KipCrossing/OpenEM/Testing/veranda/03/out.csv

i0 | i1 | i2 | i3 | i4 | i5 | i6 | i7 | i8 | i9
-2831.375 | 9287.625 | 17776.62 | 19482.62 | 13771.62 | 2856.625 | -9275.374 | -17729.37 | -19516.37 | -13822.37
18605.0 | 19074.0 | 12272.0 | 719.0 | -11310.0 | -18705.0 | -18879.0 | -12102.0 | -667.0 | 10993.0
10300.75 | -1588.25 | -12821.25 | -19103.25 | -18389.25 | -10512.25 | 1608.75 | 12986.75 | 19218.75 | 18299.75
3743.25 | 14524.25 | 19655.25 | 17359.25 | 8335.25 | -3752.75 | -14384.75 | -19630.75 | -17404.75 | -8443.75
-19773.5 | -16054.5 | -6289.5 | 5898.5 | 16090.5 | 19788.5 | 16037.5 | 6076.5 | -5927.5 | -15846.5
-4180.5 | 8013.499 | 17289.5 | 19716.5 | 14616.5 | 4064.5 | -8095.5 | -17053.5 | -19634.5 | -14736.5
18289.25 | 19406.25 | 12981.25 | 1858.25 | -10083.75 | -18036.75 | -19311.75 | -13187.75 | -2000.75 | 10086.25
11343.37 | -428.625 | -11858.62 | -18870.62 | -18729.62 | -11461.63 | 391.375 | 11910.37 | 19004.37 | 18699.37
13658.12 | 19540.12 | 18004.12 | 9536.124 | -2684.875 | -13589.87 | -19384.87 | -17911.87 | -9648.875 | 2482.125
-16816.25 | -7430.25 | 4844.75 | 15111.75 | 19589.75 | 16889.75 | 7500.75 | -4743.25 | -15080.25 | -19867.25
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
