KipCrossing/OpenEM/Testing/veranda/03/RF_calibrate.csv

Freq | Amp | Shift | tim_freq | temp
9240 | 170985 | 2.391 | 92409.24 | 23.66216
Hp | 171230.9 | 2.398835
