KipCrossing/OpenEM/Testing/veranda/04/OpenEM_data.csv

ID | Amp | Shift | Shift_out | Voltage | Temp | Humidity | CoreTemp | Hs | Hp | Wmean
0 | 504.6539 | 2.1515 | 9.869001 | 13.57218 | 20.96514 | 32.60242 | 40.24 | -502.9455 | -41.49047 | 1303274.0
1 | 278.8431 | 5.26171 | 2.979211 | 13.54805 | 20.96514 | 32.69398 | 40.56 | 82.69599 | 266.2984 | 1303029.0
2 | 109.1217 | 2.63798 | 0.3554819 | 13.53081 | 20.95178 | 32.66346 | 40.56 | -106.4111 | 24.17083 | 1303217.0
3 | 244.9536 | 4.97154 | 2.689041 | 13.53771 | 20.95178 | 32.66346 | 40.56 | 29.0268 | 243.2277 | 1302957.0
4 | 349.056 | 4.01746 | 1.734961 | 13.5446 | 20.93843 | 32.66193 | 39.92 | -161.3998 | 309.5 | 1303256.0
5 | 332.355 | 4.02089 | 1.738391 | 13.53081 | 20.90906 | 32.62989 | 40.88 | -153.0419 | 295.022 | 1303031.0
6 | 464.7512 | 4.651 | 2.368501 | 13.55839 | 20.90906 | 32.59785 | 40.88 | -38.35556 | 463.1658 | 1303068.0
7 | 292.5992 | 4.19723 | 1.914732 | 13.53081 | 20.90906 | 32.62989 | 40.88 | -105.1902 | 273.0371 | 1303009.0
8 | 395.6666 | 5.59753 | 3.315031 | 13.5446 | 20.89571 | 32.61158 | 40.88 | 193.88 | 344.9096 | 1303071.0
9 | 464.0008 | 4.47576 | 2.193261 | 13.57218 | 20.89571 | 32.58106 | 40.88 | -88.87419 | 455.4098 | 1302808.0
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
