KipCrossing/OpenEM/Testing/veranda/04/out.csv

i0 | i1 | i2 | i3 | i4 | i5 | i6 | i7 | i8 | i9
-13719.25 | -2996.25 | 9095.75 | 17725.75 | 19400.75 | 13706.75 | 2811.75 | -9186.25 | -17532.25 | -19307.25
10990.75 | 18447.75 | 18866.75 | 12147.75 | 730.75 | -11037.25 | -18584.25 | -18844.25 | -12016.25 | -702.25
18249.75 | 10207.75 | -1825.25 | -12827.25 | -18993.25 | -18078.25 | -10408.25 | 1640.75 | 12845.75 | 19187.75
3835.875 | 14440.88 | 19539.88 | 17215.87 | 8152.875 | -3937.125 | -14459.12 | -19465.12 | -17126.13 | -8198.125
19720.75 | 15868.75 | 5865.75 | -6142.25 | -15823.25 | -19450.25 | -15833.25 | -6090.25 | 5914.75 | 15968.75
-3826.625 | 8238.376 | 17219.37 | 19406.37 | 14391.37 | 3951.375 | -8216.624 | -17145.62 | -19636.63 | -14381.62
-18168.5 | -19202.5 | -12824.5 | -1538.5 | 10283.5 | 18195.5 | 19039.5 | 12858.5 | 1581.5 | -10224.5
-11022.0 | 635.0 | 12018.0 | 18963.0 | 18608.0 | 11014.0 | -733.0 | -12188.0 | -18875.0 | -18420.0
13926.5 | 19362.5 | 17543.5 | 8981.5 | -2875.5 | -13783.5 | -19352.5 | -17652.5 | -9055.5 | 2905.5
16413.25 | 6835.25 | -5150.75 | -15235.75 | -19508.75 | -16539.75 | -7008.75 | 5219.25 | 15383.25 | 19593.25
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
