KipCrossing/OpenEM/Testing/veranda/04/RF_calibrate.csv

Freq | Amp | Shift | tim_freq | temp
9230 | 171627 | 2.258 | 92307.69 | 21.05058
Hp | 171790.3 | 2.282499
