KipCrossing/OpenEM/Testing/veranda/05/OpenEM_data.csv

ID | Amp | Shift | Shift_out | Voltage | Temp | Humidity | CoreTemp | Hs | Hp | Wmean
0 | 365.0935 | 2.01394 | 9.742577 | 13.53081 | 18.15595 | 36.35309 | 38.64 | -360.3283 | -58.79435 | 1295978.0
1 | 259.9996 | 0.8359402 | 8.564577 | 13.53081 | 18.12925 | 36.35157 | 38.32 | -161.2306 | -203.9718 | 1296086.0
2 | 594.0989 | 0.5724001 | 8.301037 | 13.52392 | 18.12925 | 36.35157 | 38.64 | -286.5484 | -520.4262 | 1296431.0
3 | 720.9425 | 9.88171 | 7.610347 | 13.53081 | 18.08652 | 36.36225 | 38.64 | -49.94514 | -719.2104 | 1296140.0
4 | 288.9414 | 0.4888716 | 8.217508 | 13.51013 | 18.1426 | 36.31189 | 38.64 | -125.8938 | -260.0729 | 1296431.0
5 | 691.9755 | 0.2562599 | 7.984897 | 13.51702 | 18.09987 | 36.34851 | 38.96 | -207.5776 | -660.1072 | 1296259.0
6 | 751.5757 | 0.4098492 | 8.138487 | 13.51013 | 18.07317 | 36.31952 | 38.96 | -293.4896 | -691.9031 | 1296487.0
7 | 1003.587 | 9.89526 | 7.623897 | 13.46876 | 18.08652 | 36.27985 | 38.96 | -78.04741 | -1000.548 | 1296374.0
8 | 976.2518 | 0.15275 | 7.881387 | 13.53081 | 18.08652 | 36.29358 | 39.28 | -231.7092 | -948.3556 | 1296630.0
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
