KipCrossing/OpenEM/Testing/veranda/05/RF_calibrate.csv

Freq | Amp | Shift | tim_freq | temp
9256 | 169963 | 2.29 | 92561.98 | 18.15595
Hp | 170780.4 | 2.271363
