KipCrossing/OpenEM/Testing/veranda/06/OpenEM_data.csv

ID | Amp | Shift | Shift_out | Voltage | Temp | Humidity | CoreTemp | Hs | Hp | Wmean
0 | 55075.06 | 0.3618498 | 0.3618498 | 12.98614 | 21.77958 | 40.53407 | 42.16 | -53657.74 | 12414.1 | 1301681.0
1 | 55323.97 | 0.3590803 | 0.3590803 | 12.97925 | 21.77958 | 40.53407 | 42.16 | -53921.85 | 12376.39 | 1301405.0
2 | 55229.5 | 0.3468809 | 0.3468809 | 12.95167 | 21.77958 | 40.56458 | 42.16 | -53922.9 | 11942.29 | 1301936.0
3 | 55297.14 | 0.3640001 | 0.3640001 | 12.94478 | 21.80895 | 40.63478 | 42.8 | -53857.21 | 12536.93 | 1301509.0
4 | 55235.7 | 0.3609898 | 0.3609898 | 12.94822 | 21.80895 | 40.59358 | 42.8 | -53820.95 | 12421.23 | 1302010.0
5 | 54937.93 | 0.3691707 | 0.3691707 | 12.96546 | 21.82231 | 40.62409 | 42.16 | -53466.61 | 12629.26 | 1301631.0
6 | 55257.71 | 0.3538804 | 0.3538804 | 12.96546 | 21.80895 | 40.53864 | 42.48 | -53897.37 | 12185.54 | 1301890.0
7 | 54835.28 | 0.3634501 | 0.3634501 | 12.95167 | 21.84901 | 40.50202 | 42.16 | -53411.67 | 12413.76 | 1301641.0
8 | 55273.54 | 0.3632 | 0.3632 | 12.93788 | 21.82231 | 40.48371 | 42.16 | -53840.52 | 12504.52 | 1301947.0
9 | 54762.24 | 0.3648 | 0.3648 | 12.93099 | 21.83566 | 40.48676 | 42.16 | -53330.0 | 12442.46 | 1301665.0
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
