KipCrossing/OpenEM/Testing/veranda/06/RF_calibrate.csv

Freq | Amp | Shift | tim_freq | temp
9003 | 55239 | 0.358 | 90032.16 | 21.76623
