KipCrossing/OpenEM/Testing/veranda/07/OpenEM_data.csv

ID | Amp | Shift | Shift_out | Voltage | Temp | Humidity | CoreTemp | Hs | Hp | Wmean
0 | 55153.86 | 0.3986502 | 0.3986502 | 12.47595 | 23.94522 | 43.19219 | 44.72 | -53432.71 | 13670.89 | 1315382.0
1 | 55177.61 | 0.3985901 | 0.3985901 | 12.48974 | 23.93187 | 43.17541 | 44.72 | -53456.23 | 13674.76 | 1315152.0
2 | 55202.72 | 0.4016297 | 0.4016297 | 12.51042 | 23.95857 | 43.16625 | 44.72 | -53454.34 | 13783.1 | 1315230.0
3 | 55266.44 | 0.39904 | 0.39904 | 12.50353 | 24.0013 | 43.18456 | 45.36 | -53538.42 | 13711.91 | 1315123.0
4 | 55273.61 | 0.4010897 | 0.4010897 | 12.48284 | 23.9746 | 43.17998 | 45.36 | -53527.66 | 13782.64 | 1315268.0
5 | 55354.38 | 0.4040103 | 0.4040103 | 12.48284 | 23.9746 | 43.08385 | 45.36 | -53580.46 | 13901.13 | 1315127.0
6 | 55339.76 | 0.4022593 | 0.4022593 | 12.48974 | 24.028 | 43.11895 | 46.0 | -53581.57 | 13838.51 | 1315339.0
7 | 55324.94 | 0.4029896 | 0.4029896 | 12.49663 | 24.01465 | 43.0747 | 45.68 | -53560.86 | 13859.39 | 1315190.0
8 | 55451.03 | 0.4025106 | 0.4025106 | 12.48284 | 24.028 | 43.10522 | 45.36 | -53687.11 | 13874.82 | 1315379.0
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
