KipCrossing/OpenEM/Testing/veranda/07/RF_calibrate.csv

Freq | Amp | Shift | tim_freq | temp
9004 | 55055 | 0.397 | 90032.16 | 23.91852
