KipCrossing/OpenEM/Testing/veranda/08/OpenEM_data.csv

ID | Amp | Shift | Shift_out | Voltage | Temp | Humidity | CoreTemp | Hs | Hp | Wmean
0 | 184668.3 | 1.3105 | 1.3105 | 13.25158 | 24.60479 | 38.6389 | 39.28 | -125523.2 | 135448.4 | 1303020.0
1 | 184858.1 | 1.310061 | 1.310061 | 13.25503 | 24.59144 | 38.55497 | 39.92 | -125689.8 | 135553.0 | 1302961.0
2 | 184663.0 | 1.30923 | 1.30923 | 13.22056 | 24.57809 | 38.53819 | 39.6 | -125627.7 | 135344.4 | 1303162.0
3 | 184486.1 | 1.310181 | 1.310181 | 13.22745 | 24.56474 | 38.63432 | 39.6 | -125426.6 | 135289.7 | 1303014.0
4 | 184298.9 | 1.31014 | 1.31014 | 13.22056 | 24.60479 | 38.66636 | 40.24 | -125302.8 | 135149.2 | 1303344.0
5 | 184068.2 | 1.30898 | 1.30898 | 13.19643 | 24.57809 | 38.77623 | 40.56 | -125244.3 | 134888.7 | 1303168.0
6 | 184147.5 | 1.30695 | 1.30695 | 13.19987 | 24.57809 | 38.83116 | 40.88 | -125470.2 | 134786.9 | 1303441.0
7 | 184002.4 | 1.30775 | 1.30775 | 13.21366 | 24.56474 | 38.81742 | 40.88 | -125303.6 | 134743.7 | 1303238.0
8 | 184056.0 | 1.304939 | 1.304939 | 13.21021 | 24.57809 | 38.78996 | 40.88 | -125578.0 | 134561.5 | 1303679.0
9 | 184081.4 | 1.304361 | 1.304361 | 13.22745 | 24.57809 | 38.78996 | 40.56 | -125644.2 | 134534.3 | 1303412.0
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
