KipCrossing/OpenEM/Testing/veranda/08/RF_calibrate.csv

Freq | Amp | Shift | tim_freq | temp
9151 | 185114 | 1.314 | 91503.27 | 24.63416
