KipCrossing/OpenEM/Testing/veranda/09/OpenEM_data.csv

ID | Amp | Shift | Shift_out | Voltage | Temp | Humidity | CoreTemp | Hs | Hp | Wmean
0 | 164141.5 | 1.11001 | 1.11001 | 13.25503 | 20.71412 | 36.28901 | 40.56 | -125812.7 | 105421.1 | 1302090.0
1 | 164186.9 | 1.11056 | 1.11056 | 13.19987 | 20.68475 | 36.24323 | 40.88 | -125811.0 | 105493.8 | 1301747.0
2 | 164271.8 | 1.11013 | 1.11013 | 13.22745 | 20.67139 | 36.28443 | 40.56 | -125904.6 | 105514.3 | 1301945.0
3 | 164369.8 | 1.11221 | 1.11221 | 13.24124 | 20.65537 | 36.29663 | 41.52 | -125841.6 | 105741.8 | 1301805.0
4 | 164403.0 | 1.11198 | 1.11198 | 13.24124 | 20.64202 | 36.29663 | 40.88 | -125882.3 | 105745.0 | 1301841.0
5 | 164455.1 | 1.11226 | 1.11226 | 13.21366 | 20.61265 | 36.22339 | 41.2 | -125903.6 | 105800.6 | 1301592.0
6 | 164585.4 | 1.1125 | 1.1125 | 13.22745 | 20.58594 | 36.27527 | 41.2 | -125987.3 | 105903.4 | 1301644.0
7 | 164570.8 | 1.11305 | 1.11305 | 13.18608 | 20.55657 | 36.34241 | 41.52 | -125939.5 | 105937.6 | 1301501.0
8 | 164638.1 | 1.112949 | 1.112949 | 13.21366 | 20.55657 | 36.35614 | 41.2 | -125997.8 | 105972.9 | 1301710.0
9 | 164591.0 | 1.11232 | 1.11232 | 13.24124 | 20.52987 | 36.32563 | 41.2 | -126003.6 | 105892.8 | 1301445.0
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
