KipCrossing/OpenEM/Testing/veranda/09/RF_calibrate.csv

Freq | Amp | Shift | tim_freq | temp
9151 | 163735 | 1.107 | 91503.27 | 20.74082
