KipCrossing/OpenEM/Testing/veranda/10/OpenEM_data.csv

ID | Amp | Shift | Shift_out | Voltage | Temp | Humidity | CoreTemp | Hs | Hp | Wmean
0 | 160160.4 | 1.0684 | 1.0684 | 12.60694 | 19.95575 | 36.23255 | 39.6 | -125408.2 | 99619.92 | 1300230.0
1 | 160151.7 | 1.070169 | 1.070169 | 12.62073 | 19.93973 | 36.25696 | 39.6 | -125290.6 | 99753.86 | 1300025.0
2 | 160272.2 | 1.07519 | 1.07519 | 12.59315 | 19.93973 | 36.2295 | 40.24 | -125069.3 | 100223.9 | 1300469.0
3 | 160289.8 | 1.0713 | 1.0713 | 12.59315 | 19.897 | 36.25544 | 40.24 | -125327.6 | 99928.9 | 1300078.0
4 | 160504.3 | 1.07135 | 1.07135 | 12.60005 | 19.88365 | 36.27985 | 40.56 | -125492.3 | 100066.6 | 1300304.0
5 | 160324.3 | 1.07354 | 1.07354 | 12.59315 | 19.8703 | 36.29358 | 40.56 | -125213.9 | 100126.8 | 1299909.0
6 | 160572.7 | 1.07135 | 1.07135 | 12.56558 | 19.85428 | 36.29206 | 40.88 | -125545.8 | 100109.2 | 1300100.0
7 | 160455.0 | 1.072411 | 1.072411 | 12.57247 | 19.84093 | 36.33326 | 40.88 | -125387.0 | 100119.5 | 1299672.0
8 | 160555.6 | 1.07139 | 1.07139 | 12.55179 | 19.84093 | 36.27832 | 40.88 | -125529.9 | 100101.8 | 1300098.0
9 | 160641.4 | 1.07371 | 1.07371 | 12.58626 | 19.82758 | 36.30274 | 40.56 | -125450.8 | 100338.2 | 1299822.0
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
