KipCrossing/OpenEM/Testing/veranda/10/RF_calibrate.csv

Freq | Amp | Shift | tim_freq | temp
9151 | 159524 | 1.067 | 91503.27 | 19.98245
