KipCrossing/OpenEM/Testing/veranda/11/OpenEM_data.csv

ID | Amp | Shift | Shift_out | Voltage | Temp | Humidity | CoreTemp | Hs | Hp | Wmean
0 | 157705.7 | 0.990139 | 0.990139 | 12.21395 | 17.62455 | 55.04387 | 33.84 | -128158.5 | 91904.82 | 1287935.0
1 | 157675.5 | 0.9905699 | 0.9905699 | 12.1519 | 17.6112 | 55.00725 | 34.16 | -128109.0 | 91921.89 | 1287661.0
2 | 157725.5 | 0.9898496 | 0.9898496 | 12.10364 | 17.57915 | 55.22392 | 33.84 | -128191.3 | 91893.05 | 1288008.0
3 | 157703.6 | 0.98947 | 0.98947 | 12.06917 | 17.59785 | 55.10948 | 33.84 | -128195.4 | 91849.73 | 1287691.0
4 | 157745.7 | 0.9878702 | 0.9878702 | 12.10364 | 17.57915 | 55.1873 | 34.48 | -128321.9 | 91745.27 | 1288115.0
5 | 157512.3 | 0.9879099 | 0.9879099 | 12.04849 | 17.57915 | 55.39788 | 34.48 | -128129.7 | 91612.72 | 1287585.0
6 | 157481.7 | 0.9882598 | 0.9882598 | 12.08296 | 17.5391 | 55.51995 | 34.48 | -128084.7 | 91623.08 | 1287988.0
7 | 157536.2 | 0.9882889 | 0.9882889 | 12.09675 | 17.52308 | 55.49401 | 34.16 | -128127.4 | 91657.14 | 1287803.0
8 | 157650.1 | 0.9839699 | 0.9839699 | 12.12433 | 17.52308 | 55.43756 | 34.48 | -128468.4 | 91375.1 | 1288035.0
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
