KipCrossing/OpenEM/Testing/veranda/11/RF_calibrate.csv

Freq | Amp | Shift | tim_freq | temp
9151 | 157947 | 0.992 | 91503.27 | 17.6379
