KipCrossing/OpenEM/Testing/Calibrate_data.csv

ID | Amp | Shift | Shift_out | Voltage | Temp | Humidity | Hs | Hp | Hs | Hp | amp*math.sin(math.pi*2*sft_out/spw) | 5.7 | 2.19 | Hs2 | Hp2 | 2
0 | 11150.13 | 5.900001 | 9.5 | 11.95856 | 19.98245 | 36.89784 | 10604.4 | -3445.579 | 9414.36988588912 | 5974.53250627729 |  |  |  | 5682.11807191224 | 1846.23207788523
1 | 11110.75 | 5.9 | 9.5 | 11.92409 | 19.9691 | 36.91005 | 10566.95 | -3433.41 | 9381.11649827152 | 5953.43756231288 |  |  |  | 5662.05558799399 | 1839.71338170484
2 | 11330.16 | 5.91 | 9.51 | 11.95856 | 19.9691 | 36.99397 | 10797.41 | -3433.437 | 9604.32664431377 | 6010.77659998479 |  |  |  | 5716.58825340996 | 1857.43211878656
3 | 11312.82 | 5.9 | 9.5 | 11.94822 | 19.9691 | 36.91005 | 10759.13 | -3495.853 | 9551.72984217771 | 6061.71208277428 |  |  |  | 5765.03077622755 | 1873.17204858521
4 | 11241.93 | 5.9 | 9.5 | 11.93788 | 19.9691 | 36.92531 | 10691.71 | -3473.947 | 9491.87543553888 | 6023.72732127822 |  |  |  | 5728.9051212868 | 1861.43411175565
5 | 11461.74 | 5.89 | 9.49 | 11.95856 | 19.98245 | 36.89784 | 10878.29 | -3610.294 | 9638.68815671021 | 6202.1911003527 |  |  |  | 5898.63426129824 | 1916.58245237004
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
