KipCrossing/OpenEM/Testing/Lara/OpenEM_data.csv

ID | Amp | Shift | Shift_out | Voltage | Temp | Humidity | CoreTemp | Hs | Hp
0 | 5385.1 | 9.51 | 0.2200003 | 11.93099 | 25.33646 | 17.12978 | 34.48 | 742.0154 | 5333.734
1 | 5811.45 | 9.559999 | 0.2699995 | 11.77241 | 25.36317 | 17.07942 | 35.44 | 981.1652 | 5728.024
2 | 5598.27 | 9.52 | 0.2300005 | 11.82067 | 25.36317 | 17.09773 | 35.76 | 806.213 | 5539.914
3 | 5606.43 | 9.58 | 0.29 | 11.84825 | 25.34981 | 17.09468 | 35.76 | 1015.917 | 5513.617
4 | 5388.53 | 9.53 | 0.2399998 | 11.86894 | 25.36317 | 17.09773 | 36.4 | 809.4944 | 5327.38
5 | 5611.02 | 9.58 | 0.29 | 11.84136 | 25.37919 | 17.08095 | 36.4 | 1016.749 | 5518.131
6 | 5585.52 | 9.509999 | 0.2199993 | 11.82757 | 25.36317 | 17.07942 | 37.04 | 769.628 | 5532.242
7 | 5602.35 | 9.54 | 0.25 | 11.81033 | 25.39254 | 17.04738 | 37.04 | 876.4007 | 5533.376
8 | 5584.5 | 9.57 | 0.2799997 | 11.77931 | 25.39254 | 16.97871 | 37.04 | 977.4154 | 5498.3
9 | 5590.11 | 9.51 | 0.2200003 | 11.79999 | 25.39254 | 16.99703 | 37.04 | 770.2638 | 5536.788
10 | 5609.49 | 9.559999 | 0.2699995 | 11.89651 | 25.41924 | 16.96193 | 37.68 | 947.0678 | 5528.964
11 | 5610.509 | 9.56 | 0.2700005 | 11.82757 | 25.40589 | 16.98024 | 37.68 | 947.2433 | 5529.968
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
