KipCrossing/OpenEM/Testing/Lara/lara_data1.csv

ID | Amp | Shift | Shift_out | Voltage | Temp | Humidity | CoreTemp | Hs | Hp
0 | 19262.19 | 6.04 | 8.165 | 12.24813 | 26.22301 | 15.89838 | 34.16 | -17605.08 | 7816.209
1 | 19222.92 | 6.05 | 8.175 | 12.31019 | 26.22301 | 15.91669 | 35.12 | -17519.83 | 7910.511
2 | 19817.07 | 6.04 | 8.165 | 12.29984 | 26.19364 | 15.93194 | 34.48 | -18112.22 | 8041.368
3 | 19379.49 | 6.05 | 8.174999 | 12.24124 | 26.20966 | 15.89838 | 35.12 | -17662.53 | 7974.934
4 | 19691.61 | 6.04 | 8.165 | 12.22745 | 26.20966 | 15.94873 | 35.12 | -17997.56 | 7990.458
5 | 19707.52 | 6.04 | 8.165001 | 12.28261 | 26.19364 | 15.93194 | 35.44 | -18012.09 | 7996.922
6 | 19586.04 | 6.039999 | 8.164999 | 12.31019 | 26.20966 | 15.96704 | 35.76 | -17901.07 | 7947.61
7 | 19632.96 | 6.039999 | 8.164999 | 12.28261 | 26.20966 | 15.88159 | 36.4 | -17943.96 | 7966.65
8 | 19598.79 | 6.049999 | 8.174999 | 12.26537 | 26.20966 | 15.96704 | 36.4 | -17862.4 | 8065.178
9 | 19653.87 | 6.04 | 8.165 | 12.30674 | 26.20966 | 15.91669 | 36.72 | -17963.06 | 7975.144
10 | 19871.64 | 6.04 | 8.165 | 12.2964 | 26.20966 | 15.88159 | 36.4 | -18162.1 | 8063.511
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
