KipCrossing/OpenEM/Testing/Lara/lara_data2.csv

ID | Amp | Shift | Shift_out | Voltage | Temp | Humidity | CoreTemp | Hs | Hp
0 | 14019.88 | 5.58 | 7.705 | 12.06888 | 23.10406 | 21.49844 | 31.92 | -13903.74 | 1800.85
1 | 14496.75 | 5.58 | 7.705 | 12.09646 | 23.11742 | 21.55185 | 32.56 | -14376.66 | 1862.104
2 | 14054.67 | 5.58 | 7.705 | 12.10335 | 23.08804 | 21.48318 | 32.88 | -13938.24 | 1805.319
3 | 13941.36 | 5.59 | 7.715 | 12.04819 | 23.10406 | 21.53353 | 33.52 | -13814.34 | 1877.601
4 | 14048.3 | 5.58 | 7.705 | 12.07577 | 23.11742 | 21.55185 | 34.48 | -13931.92 | 1804.501
5 | 14056.63 | 5.58 | 7.705 | 12.05509 | 23.11742 | 21.50149 | 33.84 | -13940.19 | 1805.571
6 | 14248.89 | 5.59 | 7.715 | 12.11024 | 23.10406 | 21.53353 | 34.48 | -14119.07 | 1919.011
7 | 14519.7 | 5.58 | 7.705 | 12.11714 | 23.08804 | 21.5671 | 34.48 | -14399.42 | 1865.052
8 | 14513.07 | 5.58 | 7.705 | 12.11024 | 23.13077 | 21.58541 | 34.16 | -14392.84 | 1864.201
9 | 14483.49 | 5.58 | 7.705 | 12.06888 | 23.10406 | 21.65255 | 35.12 | -14363.51 | 1860.401
10 | 14019.39 | 5.590001 | 7.715001 | 12.10335 | 23.13077 | 21.65408 | 35.12 | -13891.66 | 1888.116
11 | 14037.24 | 5.58 | 7.705 | 12.12403 | 23.13077 | 21.67086 | 35.12 | -13920.96 | 1803.08
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
