KipCrossing/OpenEM/Testing/Lara/lara_data3.csv

ID | Amp | Shift | Shift_out | Voltage | Temp | Humidity | CoreTemp | Hs | Hp
0 | 22968.87 | 5.77 | 7.895 | 12.55149 | 23.22958 | 21.88144 | 29.68 | -22265.1 | 5642.202
1 | 23074.95 | 5.78 | 7.905 | 12.52047 | 23.24293 | 21.83108 | 30.0 | -22331.87 | 5808.692
2 | 23065.77 | 5.78 | 7.905 | 12.50323 | 23.24293 | 21.74563 | 30.32 | -22322.98 | 5806.38
3 | 22529.22 | 5.77 | 7.895 | 12.54115 | 23.24293 | 21.61135 | 30.64 | -21838.92 | 5534.204
4 | 22465.03 | 5.78 | 7.905 | 12.51013 | 23.24293 | 21.561 | 30.96 | -21741.59 | 5655.156
5 | 22493.45 | 5.78 | 7.905 | 12.5446 | 23.25628 | 21.49233 | 31.28 | -21769.09 | 5662.309
6 | 22566.48 | 5.78 | 7.905 | 12.53081 | 23.25628 | 21.42519 | 31.28 | -21839.77 | 5680.694
7 | 23115.24 | 5.77 | 7.895 | 12.51013 | 23.24293 | 21.2726 | 31.28 | -22406.98 | 5678.167
8 | 22913.28 | 5.78 | 7.905 | 12.52392 | 23.25628 | 21.22225 | 31.92 | -22175.41 | 5767.994
9 | 22471.4 | 5.78 | 7.905 | 12.50323 | 23.25628 | 21.15358 | 31.92 | -21747.75 | 5656.769
10 | 22719.48 | 5.78 | 7.905 | 12.5446 | 23.25628 | 20.99947 | 31.92 | -21987.85 | 5719.209
11 | 22882.17 | 5.78 | 7.905 | 12.55149 | 23.24293 | 20.9308 | 31.92 | -22145.3 | 5760.162
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
