KipCrossing/OpenEM/Testing/RF/Figure_1.png

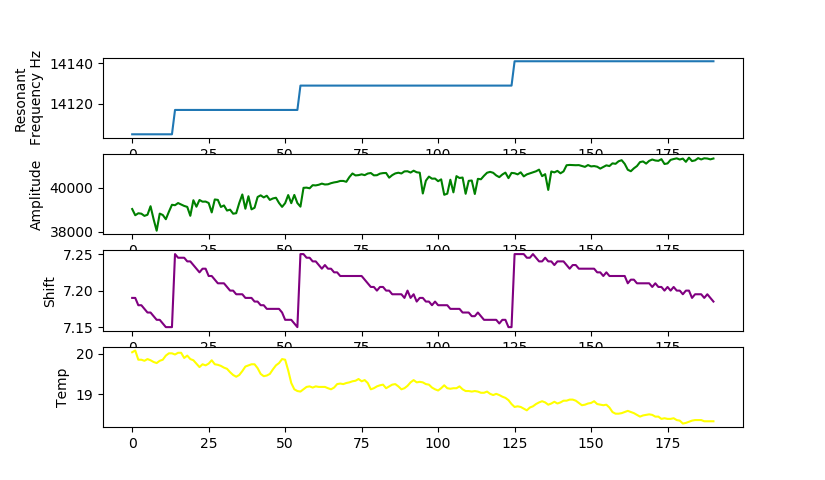
Testing/RF/Figure_1.png
