KipCrossing/OpenEM/RF_MicroPython/specialmath.py

# By Kipling Crossing
# kip.crossing@gmail.com
import math


class SpecialMath(object):
    example_data = [7013, 4020, 3648, 5009, 8975, 14013, 20992, 28005, 35020, 41425, 46042, 49082,
                    49977, 48239, 44645, 38966, 32582, 25132, 18021, 11989]

    example_data2 = [718.5, 1135.5, 1019.5, 938.5, 782.5, 612.5, 509.5, 148.5, -150.5, -386.5,
                     -528.5, -616.5, -753.5, -853.5, -980.4999, -820.5, -597.5, -361.5, -115.5, 299.5]

    def __init__(self):
        print("Message: 'Use special math!'")

    def mean(self, numb):
        return float(sum(numb)) / max(len(numb), 1)

    def gen_sin(self, length, amp, shift):
        time = []
        for x in range(length):
            time.append(x/float(length))
        y_list = []
        for x in time:
            y_list.append(amp*math.sin(math.pi*2*(x-(shift/float(length)))))
        return(y_list)

    def SSE(self, observe, predict):
        summ = 0
        for i in range(0, len(observe)):
            summ += (observe[i]-predict[i])**2
        return(summ)

    def fit_sin(self, data_list, itt):
        data_mean = self.mean(data_list)
        for d in range(0, len(data_list)):
            data_list[d] -= data_mean
        Amp_high = self.mean([data_mean - min(data_list), max(data_list) - data_mean])
        Amp_low = 0

        shft = 0
        Amp = Amp_high
        small_sse = 10E20
        small_sse_a = 10E20
        temp_shft = 0
        ALT = 0
        AHT = Amp_high

        for itteration in range(0, itt):

            for i in range(0, len(data_list)):
                if i == len(data_list):
                    t_shift = shft + float(0)/float(len(data_list)**itteration)
                else:
                    t_shift = shft + float(i)/float(len(data_list)**itteration)
                u_shift = t_shift + float(1)/float(len(data_list)**itteration)
                t_wave = self.gen_sin(len(data_list), Amp, t_shift)
                u_wave = self.gen_sin(len(data_list), Amp, u_shift)
                t_sse = self.SSE(data_list, t_wave)
                u_sse = self.SSE(data_list, u_wave)
                if self.mean([t_sse, u_sse]) < small_sse:
                    small_sse = self.mean([t_sse, u_sse])
                    temp_shft = t_shift
            shft = temp_shft

        for itteration in range(1, itt):
            for step in range(0, 9):
                amp_step_l = Amp_low + float(step)*((Amp_high - Amp_low)*2/(10.0))

                amp_step_h = amp_step_l + ((Amp_high - Amp_low)*2/(10.0))

                l_wave = self.gen_sin(len(data_list), amp_step_l, shft)
                h_wave = self.gen_sin(len(data_list), amp_step_h, shft)
                l_sse = self.SSE(data_list, l_wave)
                h_sse = self.SSE(data_list, h_wave)

                if self.mean([l_sse, h_sse]) < small_sse_a:
                    small_sse_a = self.mean([l_sse, h_sse])
                    ALT = amp_step_l
                    AHT = amp_step_h

            Amp_low = ALT
            Amp_high = AHT
            Amp = self.mean([Amp_low, Amp_high])

        return((Amp, shft))
